OpenLute/OpenLute/instruments/renaissance/OL-R1/7-course/printable/OL_R1_Nut.stl

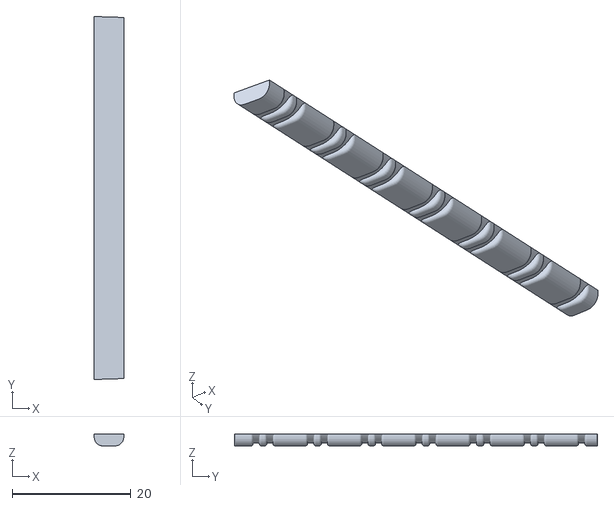
[picture p15: CAD file, 2026-08-31]
instruments/renaissance/OL-R1/7-course/printable/OL_R1_Nut.stl
5.00 x 61.1 x 2.00
